BrinoOficial/ModuloAutomacao/Imagens/IMG-2594.jpg

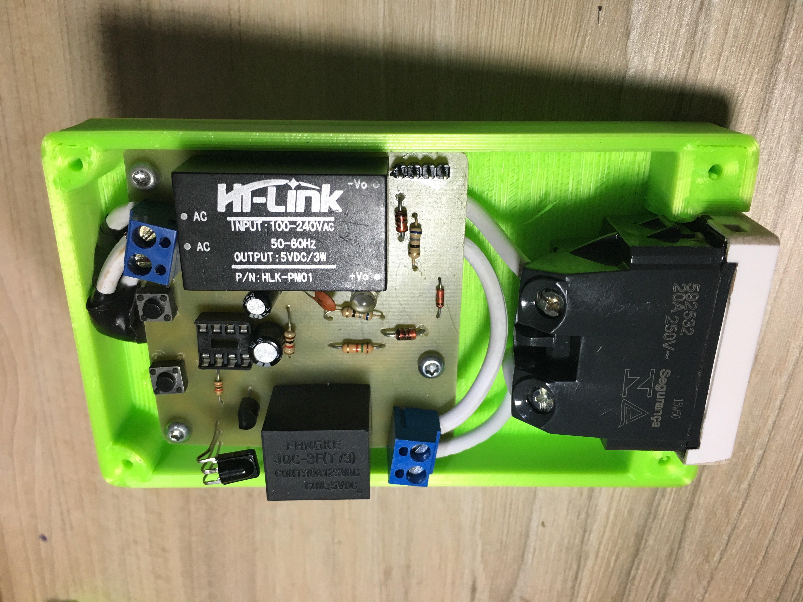
Imagens/IMG-2594.jpg
